jschrempp/LoRa_experiments/Range_Testing/Range_Test_Hub/LoRaRangeTestHub/src/tpp_LoRa.h

/*
    tpp_LoRa.h - routines for communication with the LoRa module
    created by Bob Glicksman and Jim Schrempp 2024
    as part of Team Practical Projects (tpp)

    20241212 - version 2. works on Particle Photon 2
    version 2.1 removed version as a #define
    20241222 added setAddress

*/
/*
    The block below was recommended by CoPilo. It has nothing to do with our libary.
    tpp_LoRa.h - Library for LoRa communication with the Things Plus Plus board.
    Created by Bennett Marsh, 2021.
    Released into the public domain.

*/
#ifndef tpp_LoRa_h 
#define tpp_LoRa_h

#include "tpp_LoRaGlobals.h"

#define TPP_LORA_HUB_ADDRESS 57248   // arbitrary  0 - 65535

#define TPP_LORA_MSG_GATE_SENSOR "G" // message from the sensor to the hub

#define LoRa_NETWORK_ID 18
#define LoRa_CRFOP 22             // default 22; range 1-22; 22 is max power

#define LoRa_BANDWIDTH 7         // default 7; 7:125kHz, 8:250kHz, 9:500kHz   lower is better for range but requires better
                                // frequency stability between the two devices

#define LoRa_SPREADING_FACTOR 9  // default 9;  7 - 11  larger is better for range but slower
                                // SF7 - SF9 at 125kHz, SF7 - SF10 at 250kHz, and SF7 - SF11 at 500kHz

#define LoRa_CODING_RATE 1       // default 1; 1 is faster; [1: 4/5, 2: 4/6, 3: 4/7, 4: 4/8] This can result in
                                // small signal gains at the limit of reception, but more symbols are sent for each character.

#define LoRa_PREAMBLE 12         // 12 max unless network number is 18; 

// class for the LoRa module
class tpp_LoRa
{
private:
    /* data */
    void clearConfigVariables();
    void clearClassVariables();
    void blinkLED(int ledpin, int number, int delayTimeMS) ;

    String LoRaStringBuffer;
    int isLoRaAwake = true; // true = awake, false = asleep

    // function to send AT commands to the LoRa module
    // returns 0 if successful, 1 if error, -1 if no response
    // prints message and result to the serial monitor
    int sendCommand(const String& command);

    void debugPrint(const String& message);
    void debugPrintNoHeader(const String& message);
    void debugPrintln(const String& message);

public:
    // Do some class initialization stuff
    // and test communication to the LoRa
    int begin();
    
    // set just the device address
    bool setAddress(unsigned int deviceAddress);

    // Initialize the LoRa module with settings found in the tpp_LoRa.h file
    bool configDevice(int devAddress);

    // Read current settings and print them to the serial monitor
    //  If error then return false
    bool readSettings(); 

    // check for a received message from the LoRa module. status in receivedMessageState
    // if successful, the received data is stored in the receivedData variable
    // and other class variables. If not, the class variables are set to default
    void checkForReceivedMessage();

    // function to transmit a message to another LoRa device
    // returns 0 if successful, 1 if error, -1 if no response
    // prints message and result to the serial monitor
    // XXX NOTE: when I changed this to an int for the address, the ATmega328 code broke
    // XXX so I changed it back to a string. I don't know why yet.
    int transmitMessage(long int toAddress, const String& message);
    // xxx add number or retries and a string refernce for the response
    // xxx we need to discuss this

    // function puts LoRa to sleep. LoRa will awaken when sent
    // a command.  Returns 0 if successful, 1 if error
    int sleep();

    // function to wake up the LoRa module from a low power sleep
    // returns 0 if successful, 1 if error
    // called implicitly by other methods when needed
    int wake();
    
    // class variables
    int receivedMessageState = 0; // 0 = no message, 1 = message received, -1 = error
    String UID;
    String receivedData; // xxx why do we need a receive buffer? Reuse the LoRaStringBuffer
    String payload;
    int RSSI; 
    int SNR; 
    int LoRaNetworkID;
    int LoRaBandwidth;
    int LoRaSpreadingFactor;
    int LoRaCodingRate;
    int LoRaPreamble;  
    int LoRaCRFOP;
    int LoRaDeviceAddress;
    int ReceivedDeviceAddress;

};


#endif
